denjhang/RE2-YM2413/v0.6/sshot-20241017-232652.png

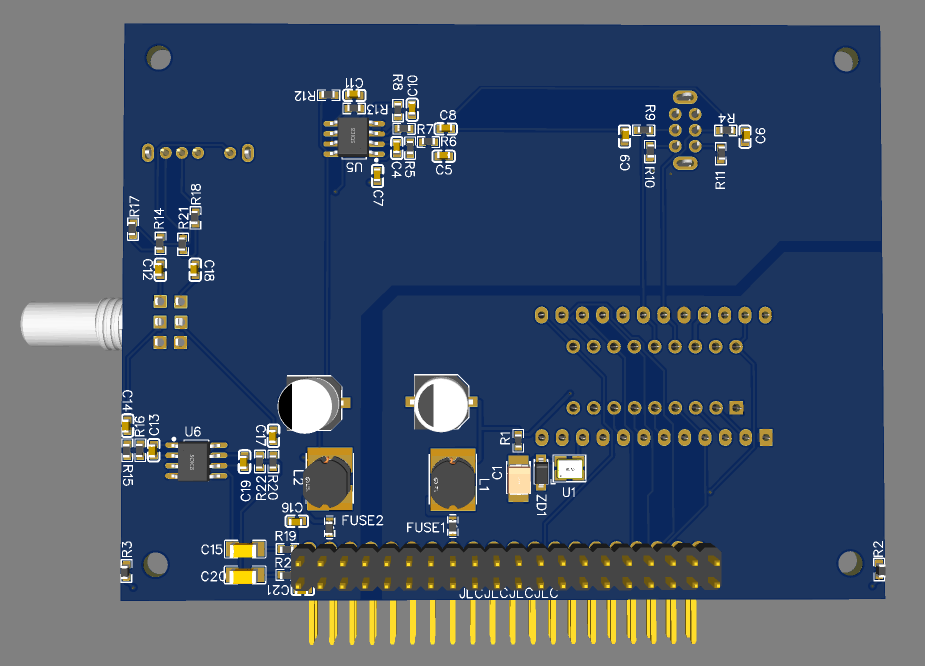
v0.6/sshot-20241017-232652.png
