denjhang/RE2-YM2413/原版图片/RE1-YM2413-2-300x211.jpg

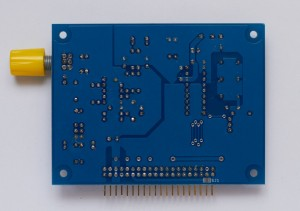
原版图片/RE1-YM2413-2-300x211.jpg
