denjhang/RE2-YM2413/原版图片/RE1-YM2413-1024x681.jpg

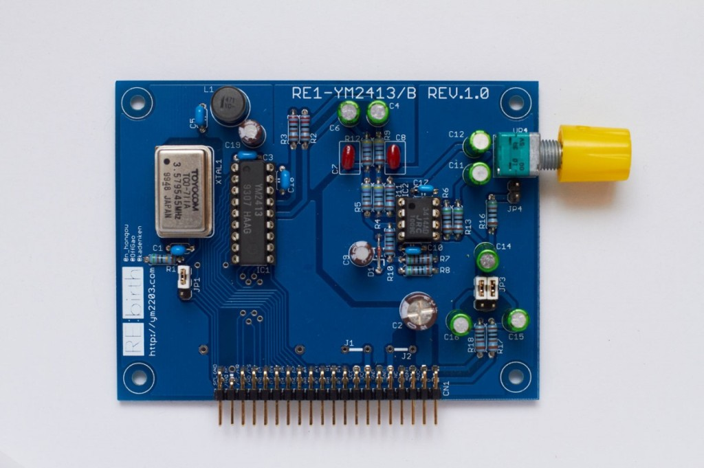
原版图片/RE1-YM2413-1024x681.jpg
